maelh/radio-frequency-prototype-boards/equipment/RF_Demo_Kit/7 - RC series circuit.png

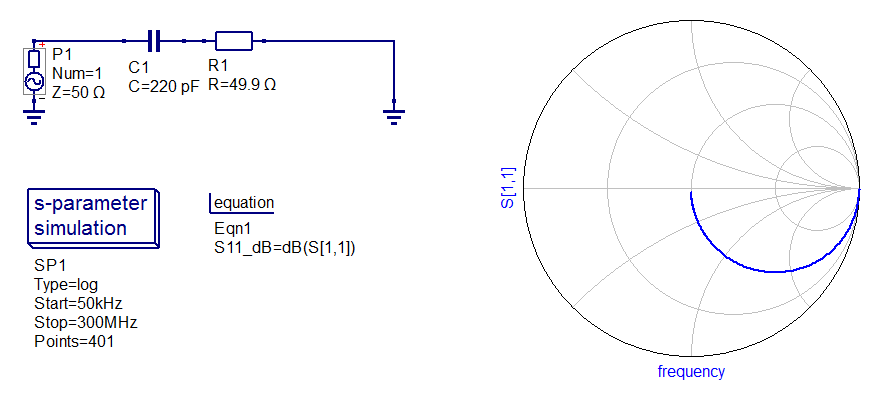
equipment/RF_Demo_Kit/7 - RC series circuit.png
